mugju/kpu_energy/Database/ERD1.png

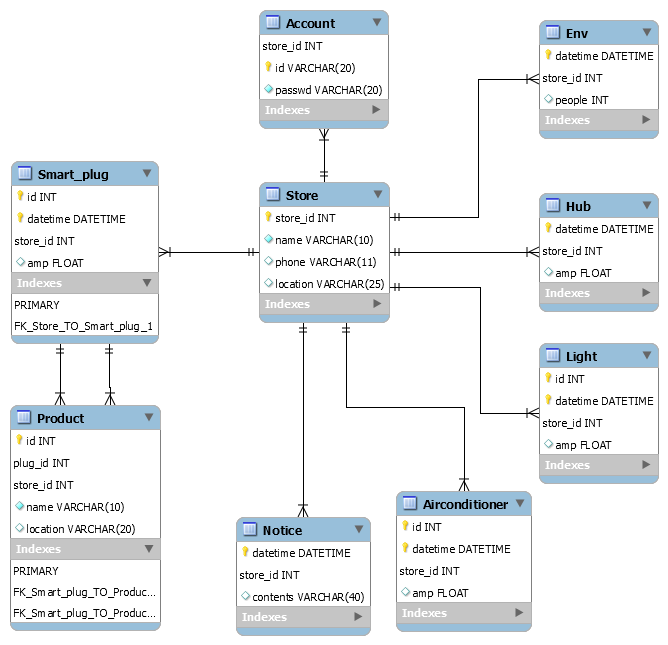
Database/ERD1.png
