mugju/kpu_energy/Database/ERD2.png

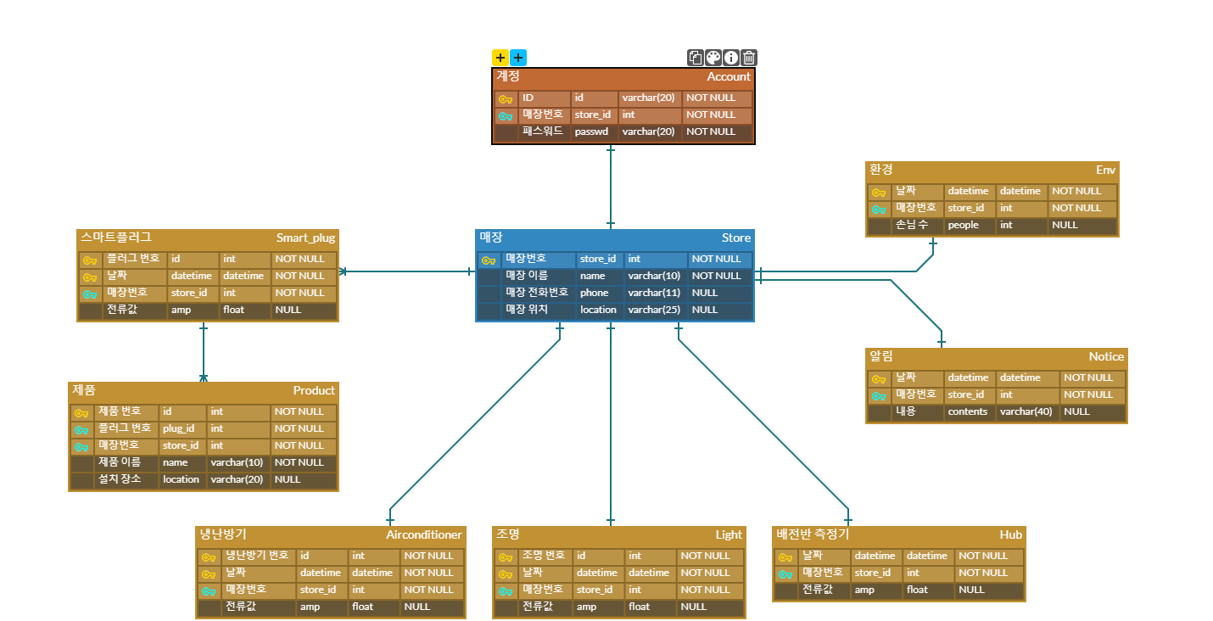
Database/ERD2.png
