mugju/kpu_energy/Hardware 3D file/3d 모델링 최신/졸작 모델링/배전반 천장.stl

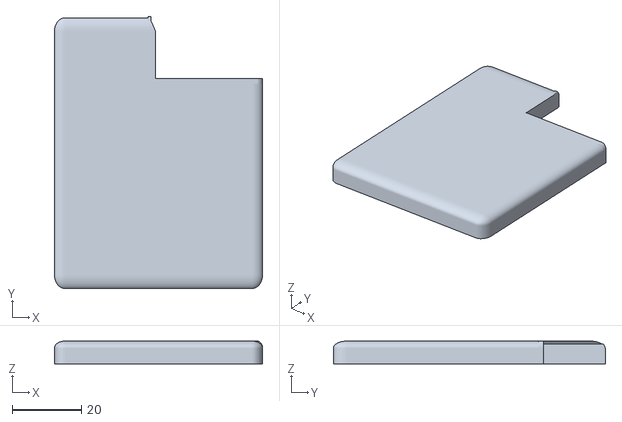
[picture p158: CAD file, 2021-08-19]
Hardware 3D file/3d 모델링 최신/졸작 모델링/배전반 천장.stl
60.0 x 78.4 x 6.60
