mugju/kpu_energy/Hardware 3D file/3d 모델링 최신/졸작 모델링/1층 천장.stl

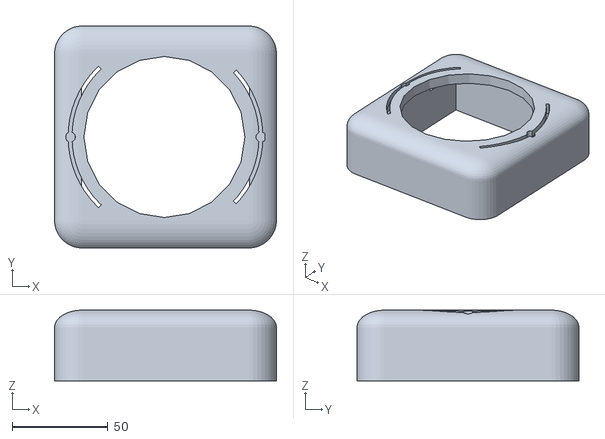
[picture p159: CAD file, 2021-08-19]
Hardware 3D file/3d 모델링 최신/졸작 모델링/1층 천장.stl
116.0 x 116.0 x 37.0
