mugju/kpu_energy/Hardware 3D file/3d 모델링 최신/졸작 모델링/배전반 전체.stl

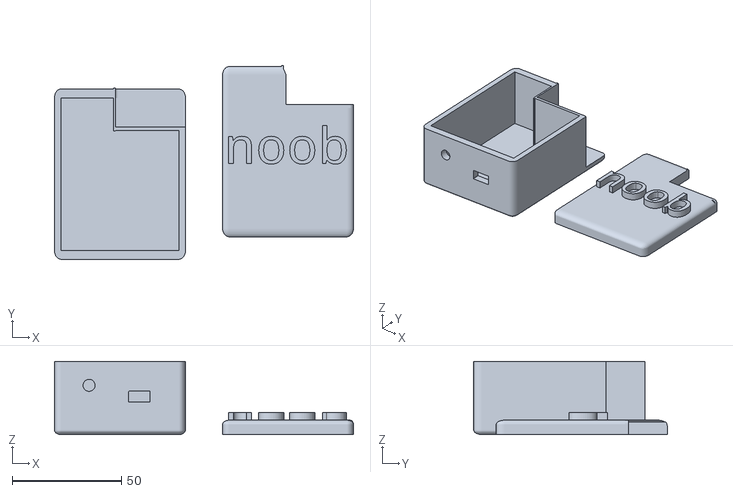
[picture p160: CAD file, 2021-08-19]
Hardware 3D file/3d 모델링 최신/졸작 모델링/배전반 전체.stl
137.0 x 88.7 x 33.5
